RetroNynjah/1541-Switchless-Multi-ROM/rev1.1/images/1541 Multi-ROM Rev1.1 bottom.png

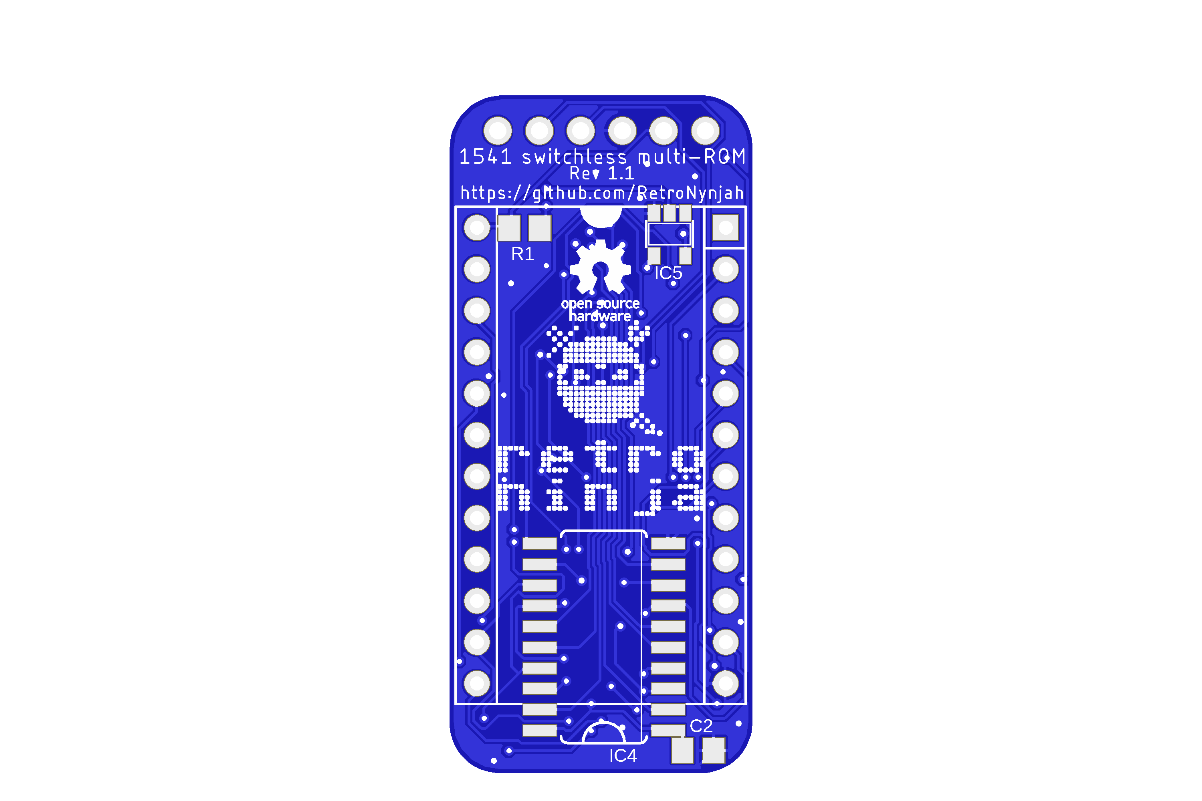
rev1.1/images/1541 Multi-ROM Rev1.1 bottom.png
